antmicro/environment-sensor/assets/previews/layer0.png

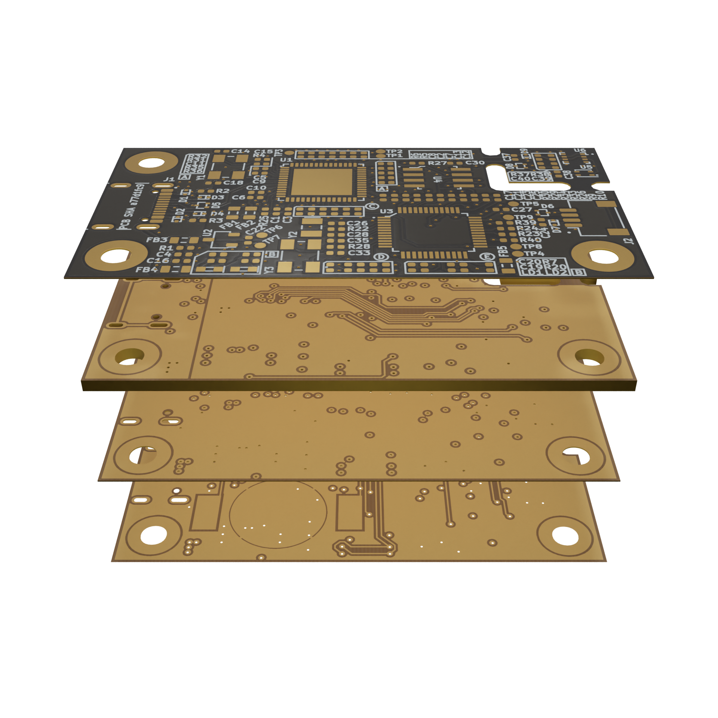
assets/previews/layer0.png
