antmicro/environment-sensor/assets/previews/layer1.png

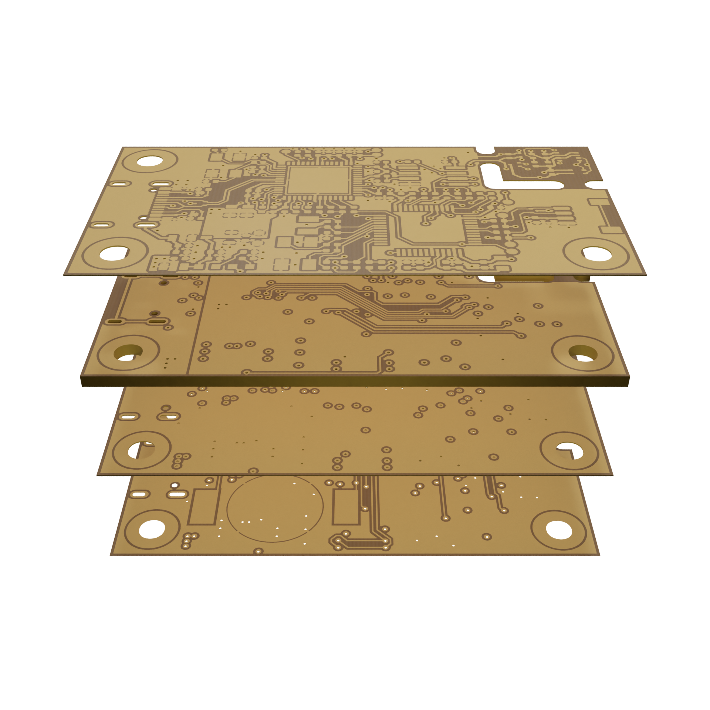
assets/previews/layer1.png
