antmicro/environment-sensor/assets/previews/layer2.png

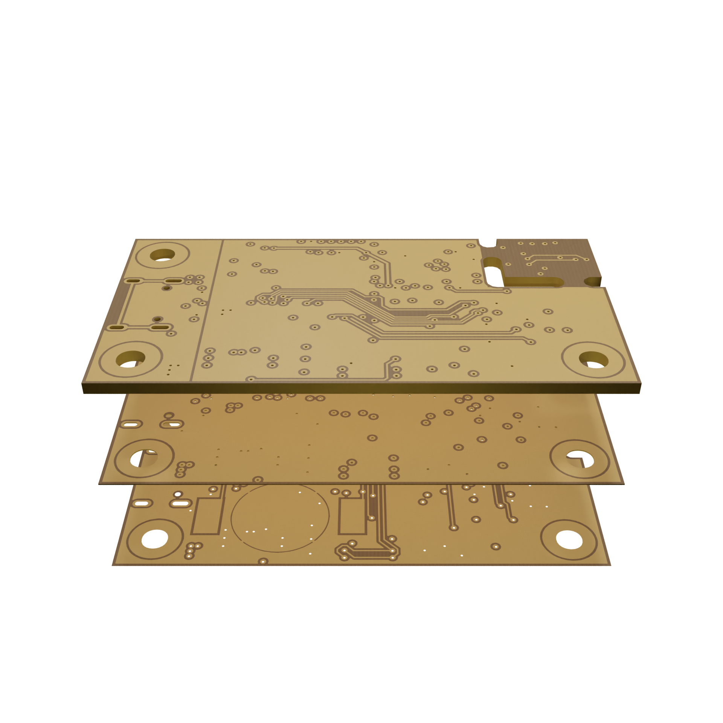
assets/previews/layer2.png
