antmicro/environment-sensor/assets/previews/layer3.png

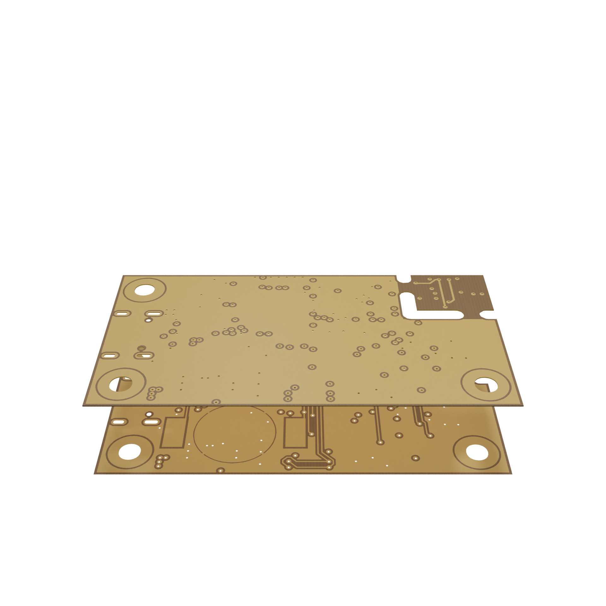
assets/previews/layer3.png
