antmicro/environment-sensor/assets/previews/layer4.png

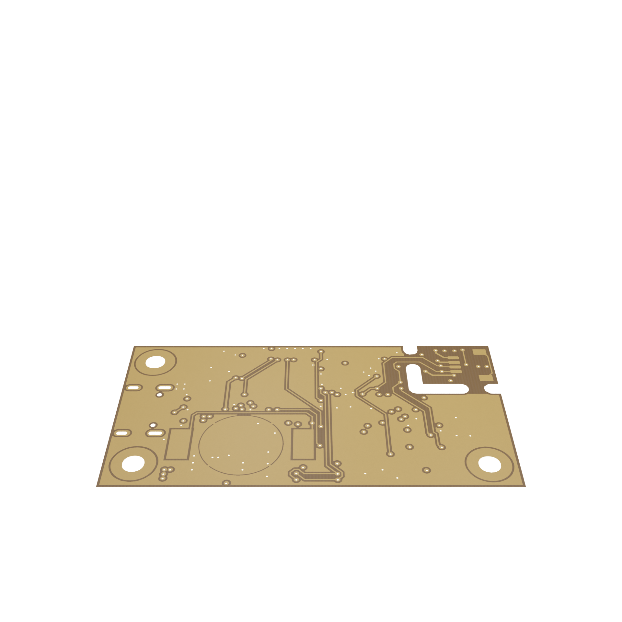
assets/previews/layer4.png
