antmicro/environment-sensor/assets/previews/leftB.png

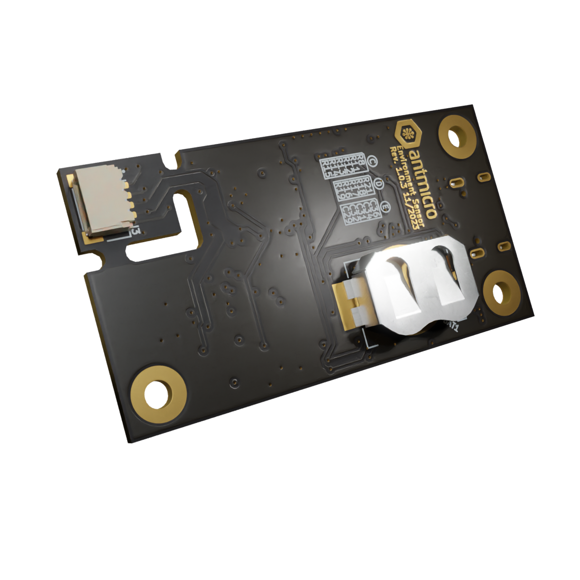
assets/previews/leftB.png
