antmicro/environment-sensor/assets/previews/orthoB.png

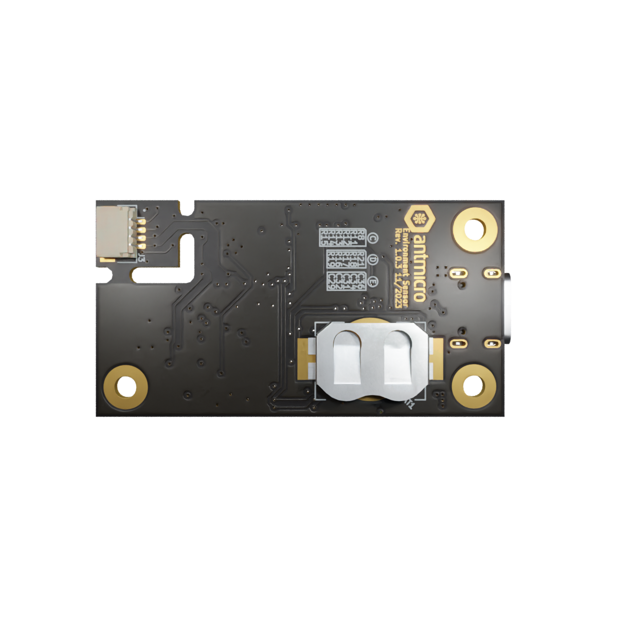
assets/previews/orthoB.png
