antmicro/environment-sensor/assets/previews/orthoT.png

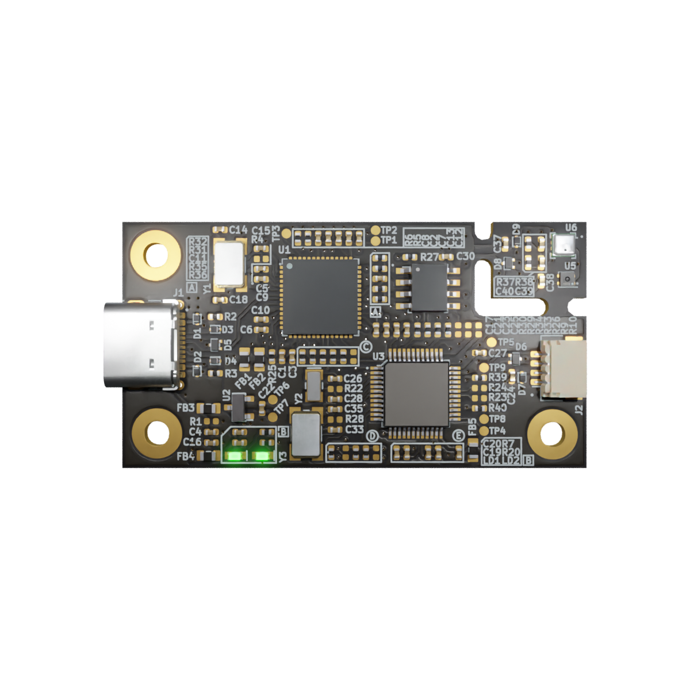
assets/previews/orthoT.png
