antmicro/environment-sensor/assets/previews/photoB.png

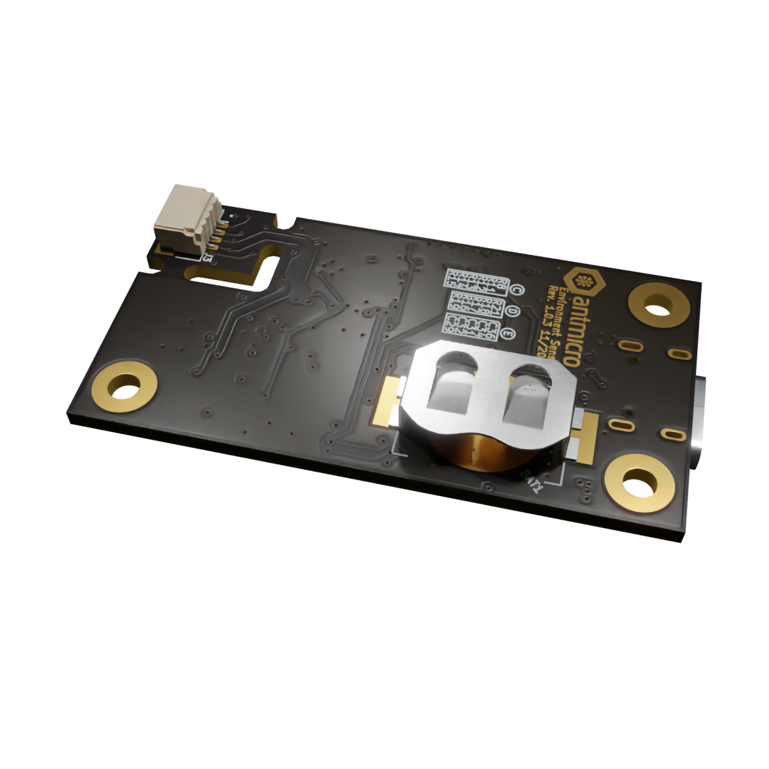
assets/previews/photoB.png
