antmicro/environment-sensor/assets/previews/photoT.png

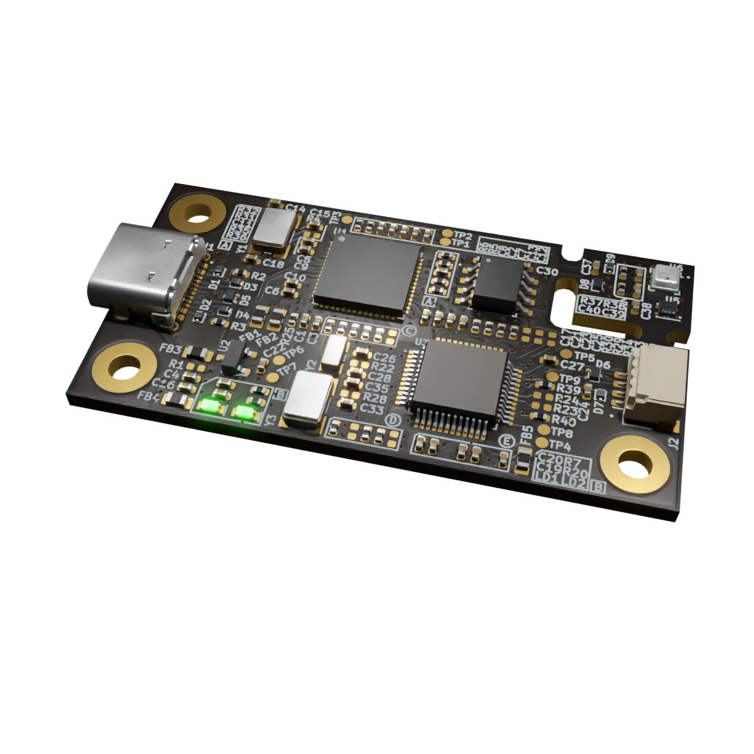
assets/previews/photoT.png
