antmicro/environment-sensor/assets/previews/rightB.png

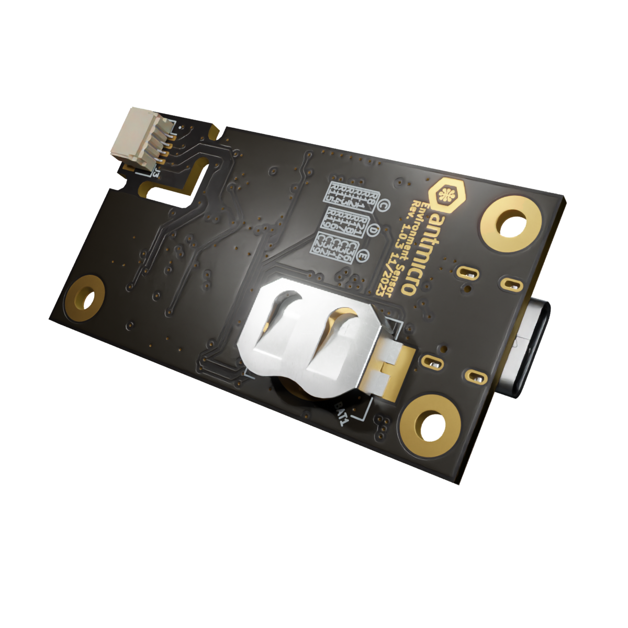
assets/previews/rightB.png
